ramonimbao/dactyl-ez2print/STL/right-hand/RH_Column_TGB.stl

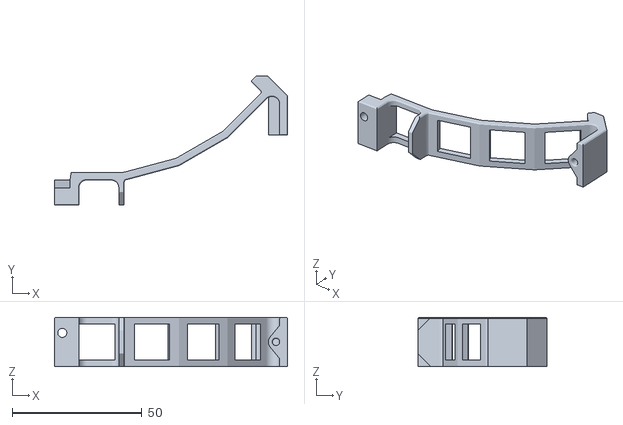
[picture p22: CAD file, 2019-11-17]
STL/right-hand/RH_Column_TGB.stl
89.8 x 49.9 x 19.1
